davischris/OpenAC1/PIC32Terminal/src/vt100.c

/****************************************************************************************
 vt100.c

	vt100 decoder for the VT100 Terminal program


	Copyright (C) 2014 Geoff Graham (projects@geoffg.net)
	All rights reserved.

	This file and the program created from it are FREE FOR COMMERCIAL AND
	NON-COMMERCIAL USE as long as the following conditions are aheared to.

	Copyright remains Geoff Graham's, and as such any Copyright notices in the
	code are not to be removed.  If this code is used in a product, Geoff Graham
	should be given attribution as the author of the parts used.  This can be in
	the form of a textual message at program startup or in documentation (online
	or textual) provided with the program or product.

	Redistribution and use in source and binary forms, with or without modification,
	are permitted provided that the following conditions  are met:
	1. Redistributions of source code must retain the copyright notice, this list
	   of conditions and the following disclaimer.
	2. Redistributions in binary form must reproduce the above copyright notice, this
	   list of conditions and the following disclaimer in the documentation and/or
	   other materials provided with the distribution.
	3. All advertising materials mentioning features or use of this software must
	   display the following acknowledgement:
	   This product includes software developed by Geoff Graham (projects@geoffg.net)

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
	The licence and distribution terms for any publically available version or
	derivative of this code cannot be changed.  i.e. this code cannot simply be copied
	and put under another distribution licence (including the GNU Public Licence).
****************************************************************************************/


#define _SUPPRESS_PLIB_WARNING
#define _DISABLE_OPENADC10_CONFIGPORT_WARNING

#include <p32xxxx.h>
#include <plib.h>
#include <string.h>
#include <ctype.h>
#include <stdio.h>
#include "Terminal.h"
#include "video.h"
#include "vt100.h"

#define VTBUF_SIZE  40
unsigned char vtbuf[VTBUF_SIZE + 1];                                // buffer for chars waiting to be decoded
int vtcnt;                                                          // count of the number of chars in vtbuf

int arg[8], argc;                                                   // arguments to a command

struct s_cmdtbl {                                                   // structure of the command table
    char *name;                                                     // the string
    int mode;                                                       // 1 = ANSI only, 2 = VT52, 3 = both
    void (*fptr)(void);                                             // pointer to the function that will interpret that command
};
int CmdTblSize;
extern const struct s_cmdtbl cmdtbl[];

int mode;                                                           // current mode.  can be VT100 or VT52

int AttribUL, AttribRV, AttribInvis;                                // attributes that can be turned on/off
int SaveX, SaveY, SaveUL, SaveRV, SaveInvis, SaveFontNbr;           // saved attributes that can be restored

void VT100Putc(char c) {
    int cmd, i, j, partial;

    if(vtcnt >= VTBUF_SIZE) return;
    vtbuf[vtcnt++] = c;
    partial = false;

    while(vtcnt) {
        for(cmd = 0; cmd < CmdTblSize; cmd++) {
            if((cmdtbl[cmd].mode & mode) && *cmdtbl[cmd].name == *vtbuf) {   // check the mode then a quick check of the first char
                arg[0] = argc = 0;
                for(j = i = 1; cmdtbl[cmd].name[i] && j < vtcnt; i++, j++) {
                    if(cmdtbl[cmd].name[i] == '^') {
                        arg[argc++] = vtbuf[j] - 31;
                    } else if(cmdtbl[cmd].name[i] == '@') {
                        arg[argc] = 0;
                        while(isdigit(vtbuf[j]))
                            arg[argc] = arg[argc] * 10 + (vtbuf[j++] - '0');
                        j--;                                        // correct for the overshoot, so that the next loop looks at the next char
                        argc++;
                    } else if(cmdtbl[cmd].name[i] != vtbuf[j])
                            goto nextcmd;                           // compare failed, try the next command
                }
                if(cmdtbl[cmd].name[i] == 0) {                      // compare succeded, we have found the command
                    vtcnt = 0;                                      // clear all chars in the queue
                    cmdtbl[cmd].fptr();                             // and execute the command
                    return;
                } else
                    partial = true;                                 // partial compare so set a flag to indicate this
            }
            nextcmd:
            continue;
        }
        if(!partial) {                                              // we have searched the table and have not even found a partial match
            VideoPutc(*vtbuf);                                      // so send the oldest char off
            memcpy(vtbuf, vtbuf + 1, vtcnt--);                      // and shift down the table
        } else
            return;                                                 // have a partial match so keep the characters in the buffer
    }                                                               // keep looping until the buffer is empty
}


void VideoPrintString(char *p) {
    while(*p) VideoPutc(*p++);
}


// utility function to move the cursor
void CursorPosition(int x, int y) {
    ShowCursor(false);                                              // turn off the cursor to prevent it from getting confused

    CursorX = (fontWidth * fontScale) * (x - 1);
    if(CursorX < 0) CursorX = 0;
    if(CursorX > HRes - (fontWidth * fontScale)) CursorX = HRes - (fontWidth * fontScale);

    CursorY = (fontHeight * fontScale) * (y - 1);
    if(CursorY < 0) CursorY = 0;
    if(CursorY > VRes - (fontHeight * fontScale)) CursorY = VRes - (fontHeight * fontScale);

    CharPosX = (CursorX / (fontWidth * fontScale)) + 1;				// update the horizontal character position
    CharPosY = (CursorY / (fontHeight * fontScale)) + 1;			// update the horizontal character position
}



// cursor up one or more lines
void cmd_CurUp(void) {
    if(argc == 0 || arg[0] == 0) arg[0] = 1;
    CursorPosition(CharPosX, CharPosY - arg[0]);
}



// cursor down one or more lines
void cmd_CurDown(void) {
    if(argc == 0 || arg[0] == 0) arg[0] = 1;
    CursorPosition(CharPosX, CharPosY + arg[0]);
}



// cursor left one or more chars
void cmd_CurLeft(void) {
    if(argc == 0 || arg[0] == 0) arg[0] = 1;
    CursorPosition(CharPosX - arg[0], CharPosY);
}


// cursor right one or more chars
void cmd_CurRight(void) {
    if(argc == 0 || arg[0] == 0) arg[0] = 1;
    CursorPosition(CharPosX + arg[0], CharPosY);
}


// cursor home
void cmd_CurHome(void) {
    CursorPosition(1, 1);
}


// position cursor
void cmd_CurPosition(void) {
    if(argc < 1 || arg[0] == 0) arg[0] = 1;
    if(argc < 2 || arg[1] == 0) arg[1] = 1;
    CursorPosition(arg[1], arg[0]);                                 // note that the argument order is Y, X
}


// enter VT52 mode
void cmd_VT52mode(void) {
    mode = VT52;
}


// enter VT100 mode
void cmd_VT100mode(void) {
    mode = VT100;
}


// clear to end of line
void cmd_ClearEOL(void) {
    int x, y;
    ShowCursor(false);                                              // turn off the cursor to prevent it from getting confused
    for(y = CursorY; y < CursorY + (fontHeight * fontScale); y++)
        for(x = CursorX; x < HRes; x++)
            plot(x, y, 0);
}


// clear to end of screen
void cmd_ClearEOS(void) {
    int y, n;
    cmd_ClearEOL();
    y = CursorY + (fontHeight * fontScale);
    n = VBuf*(HBuf/8) - (y * (HBuf/8));
	if(y < VBuf) memset((char *)VideoBuf + (y * (HBuf/8)), 0, n);
}


// clear from the beginning of the line to the cursor
void cmd_ClearBOL(void) {
    int x, y;
    ShowCursor(false);                                              // turn off the cursor to prevent it from getting confused
    for(y = CursorY; y < CursorY + (fontHeight * fontScale); y++)
        for(x = 0; x < CursorX; x++)
            plot(x, y, 0);
}


// clear from home to the cursor
void cmd_ClearBOS(void) {
    int x, y;
    cmd_ClearBOL();
    for(y = CursorY - 1; y >= 0; y--)
        for(x = 0; x < HRes; x++)
            plot(x, y, 0);
}


// turn the cursor off
void cmd_CursorOff(void) {
    CursorOff = true;
}


// turn the cursor on
void cmd_CursorOn(void) {
    CursorOff = false;
}


// save the current attributes
void cmd_ClearLine(void) {
    cmd_ClearBOL();
    cmd_ClearEOL();
}


// save the current attributes
void cmd_CurSave(void) {
    SaveX = CharPosX;
    SaveY = CharPosY;
    SaveUL = AttribUL;
    SaveRV = AttribRV;
    SaveInvis = AttribInvis;
    SaveFontNbr = fontNbr;
}


// restore the saved attributes
void cmd_CurRestore(void) {
    if(SaveFontNbr == -1) return;
    CursorPosition(SaveX, SaveY);
    AttribUL = SaveUL;
    AttribRV = SaveRV;
    AttribInvis = SaveInvis;
    initFont(SaveFontNbr);
}


// set the keyboard to numbers mode
void cmd_SetNumLock(void) {
    NumLock = false;
    setLEDs(CapsLock,  false, 0);
}


// set the keyboard to arrows mode
void cmd_ExitNumLock(void) {
    NumLock = true;
    setLEDs(CapsLock,  true, 0);
}


// respond as a VT52
void cmd_VT52ID(void) {
    putSerialString("\033[/Z");
}


// respond as a VT100 thats OK
void cmd_VT100OK(void) {
    putSerialString("\033[0n");
}


// respond as a VT100 with no optiond
void cmd_VT100ID(void) {
    putSerialString("\033[?1;0c");    // vt100 with no options
}


// reset the terminal
void cmd_Reset(void) {
    mode = VT100;
    initFont(1);
    ConfigBuffers(Option[O_LINES24]);
    ShowCursor(false);                                              // turn off the cursor to prevent it from getting confused
    ClearScreen();
    CursorPosition(1, 1);
    AttribUL = 0;
    AttribRV = 0;
    AttribInvis = 0;
    SaveFontNbr = -1;
}


// control the keyboard leds
void cmd_LEDs(void) {
    static int led1 = 0;
    static int led2 = 0;
    static int led3 = 0;

    if(arg[0] == 0) led1 = led2 = led3 = 0;
    if(arg[0] == 2) led1 = 1;
    if(arg[0] == 1) led2 = 1;
    if(arg[0] == 3) led3 = 1;
    setLEDs(led1, led2, led3);
}


// set attributes
void cmd_Attributes(void) {
    ShowCursor(false);                                              // turn off the cursor to prevent it from getting confused
    if(arg[0] == 0) {
        AttribUL = AttribRV = AttribInvis = 0;
        initFont(1);
    }
    if(arg[0] == 4) AttribUL = 1;
    if(arg[0] == 3) initFont(2);
    if(arg[0] == 7) AttribRV = 1;
    if(arg[0] == 6) initFont(3);
    if(arg[0] == 8) AttribInvis = 1;
}


// respond with the current cursor position
void cmd_ReportPosition(void) {
    char s[20];
    sprintf(s, "\033[%d;%dR", CharPosY, CharPosX);
    putSerialString(s);
}


// do a line feed
void cmd_Lf(void) {
    VideoPutc('\n');
}


// do a line feed
void cmd_LineFeed(void) {
    VideoPutc('\n');
}


// do an upwards line feed with a reverse scroll
void cmd_ReverseLineFeed(void) {
    ShowCursor(false);                                              // turn off the cursor to prevent it from getting confused
    if(CharPosY > 1)
        CursorPosition(CharPosX, CharPosY - 1);
    else
        ScrollDown();
}


// turn on automatic line wrap, etc
void cmd_SetMode(void) {
    if(arg[0] == 7) AutoLineWrap = true;
    if(arg[0] == 9 && vga) {
        cmd_CurHome();
        ConfigBuffers(true);
        ShowCursor(false);                                              // turn off the cursor to prevent it from getting confused
        ClearScreen();
        CursorPosition(1, 1);
    }
}


// turn off automatic line wrap, etc
void cmd_ResetMode(void) {
    if(arg[0] == 7) AutoLineWrap = false;
    if(arg[0] == 9 && vga) {
        ConfigBuffers(false);
        ShowCursor(false);                                              // turn off the cursor to prevent it from getting confused
        ClearScreen();
        CursorPosition(1, 1);
    }
}


// draw graphics
void cmd_Draw(void) {
//    if(Display24Lines) {
//        arg[2] = (arg[2]/3)*2;
//        arg[4] = (arg[4]/3)*2;
//    }
    if(arg[0] == 1) DrawLine(arg[1], arg[2], arg[3], arg[4], 1);
    if(arg[0] == 2) DrawBox(arg[1], arg[2], arg[3], arg[4], 0, 1);
    if(arg[0] == 3) DrawBox(arg[1], arg[2], arg[3], arg[4], 1, 1);
    if(arg[0] == 4) DrawCircle(arg[1], arg[2], arg[3], 0, 1, vga ? 1.14 : 1.0);
    if(arg[0] == 5) DrawCircle(arg[1], arg[2], arg[3], 1, 1, vga ? 1.14 : 1.0);
}


// do nothing for escape sequences that are not implemented
void cmd_NULL(void) {}



/***************************************************************************************************************************************
 The command table
 This is scanned from top to bottom by VT100Putc()
 Characters are matched exactly (ie, case sensitive) except for the @ character which is a wild card character representing
 zero or more decimal characters of an argument and ^ which represents a single char and the value returned is the char - 31
 **************************************************************************************************************************************/
const struct s_cmdtbl cmdtbl[]  = {
    { "\033A",          VT52,       cmd_CurUp },
    { "\033B",          VT52,       cmd_CurDown },
    { "\033C",          VT52,       cmd_CurRight },
    { "\033D",          VT52,       cmd_CurLeft },
    { "\033H",          VT52,       cmd_CurHome },
    { "\033I",          VT52,       cmd_ReverseLineFeed },
    { "\033[^^",        VT52,       cmd_CurPosition },

    { "\033J",          VT52,       cmd_ClearEOS },
    { "\033K",          VT52,       cmd_ClearEOL },

    { "\033>",          VT52,       cmd_SetNumLock },
    { "\033=",          VT52,       cmd_ExitNumLock },

    { "\033[Z",         VT52,       cmd_VT52ID },
    { "\033<",          VT52,       cmd_VT100mode },
    { "\033F",          VT52,       cmd_NULL },
    { "\033G",          VT52,       cmd_NULL },

    { "\033[K",         VT100,      cmd_ClearEOL },
    { "\033[J",         VT100,      cmd_ClearEOS },
    { "\033[0K",        VT100,      cmd_ClearEOL },
    { "\033[1K",        VT100,      cmd_ClearBOL },
    { "\033[2K",        VT100,      cmd_ClearLine },
    { "\033[0J",        VT100,      cmd_ClearEOS },
    { "\033[1J",        VT100,      cmd_ClearBOS },
    { "\033[2J",        VT100,      ClearScreen },

    { "\033[?25l",      VT100,      cmd_CursorOff },
    { "\033[?25h",      VT100,      cmd_CursorOn },

    { "\033[@A",        VT100,      cmd_CurUp },
    { "\033[@B",        VT100,      cmd_CurDown },
    { "\033[@C",        VT100,      cmd_CurRight },
    { "\033[@D",        VT100,      cmd_CurLeft },
    { "\033[@;@H",      VT100,      cmd_CurPosition },
    { "\033[@;@f",      VT100,      cmd_CurPosition },
    { "\033[H",         VT100,      cmd_CurHome },
    { "\033[f",         VT100,      cmd_CurHome },
    { "\0337",          VT100,      cmd_CurSave },
    { "\0338",          VT100,      cmd_CurRestore },
    { "\0336n",         VT100,      cmd_ReportPosition },

    { "\033D",          VT100,      cmd_LineFeed },
    { "\033M",          VT100,      cmd_ReverseLineFeed },
    { "\033E",          VT100,      cmd_Lf },
    { "\033[?@h",       VT100,      cmd_SetMode },
    { "\033[?@l",       VT100,      cmd_ResetMode },

    { "\033[>",         VT100,      cmd_SetNumLock },
    { "\033[=",         VT100,      cmd_ExitNumLock },

    { "\033[Z@;@;@;@;@Z",VT100,     cmd_Draw },
    { "\033[Z@;@;@;@Z",  VT100,     cmd_Draw },

    { "\033[@m" ,       VT100,      cmd_Attributes },
    { "\033[@q" ,       VT100,      cmd_LEDs },
    { "\033c" ,         BOTH,       cmd_Reset },
    { "\033[c" ,        VT100,      cmd_VT100ID },
    { "\033[0c" ,       VT100,      cmd_VT100ID },
    { "\033[5n" ,       VT100,      cmd_VT100OK },
    { "\033[?2l",       VT100,      cmd_VT52mode },
};                                                                  // must be last in the table



void initVT100(void) {
    mode = VT100;
    vtcnt = 0;
    CmdTblSize =  (sizeof(cmdtbl)/sizeof(struct s_cmdtbl));
    SaveFontNbr = -1;
}
